Elektroarzt/floragrow/Sense PS/assets/FloraGrow Sense PS PCB bottom.png

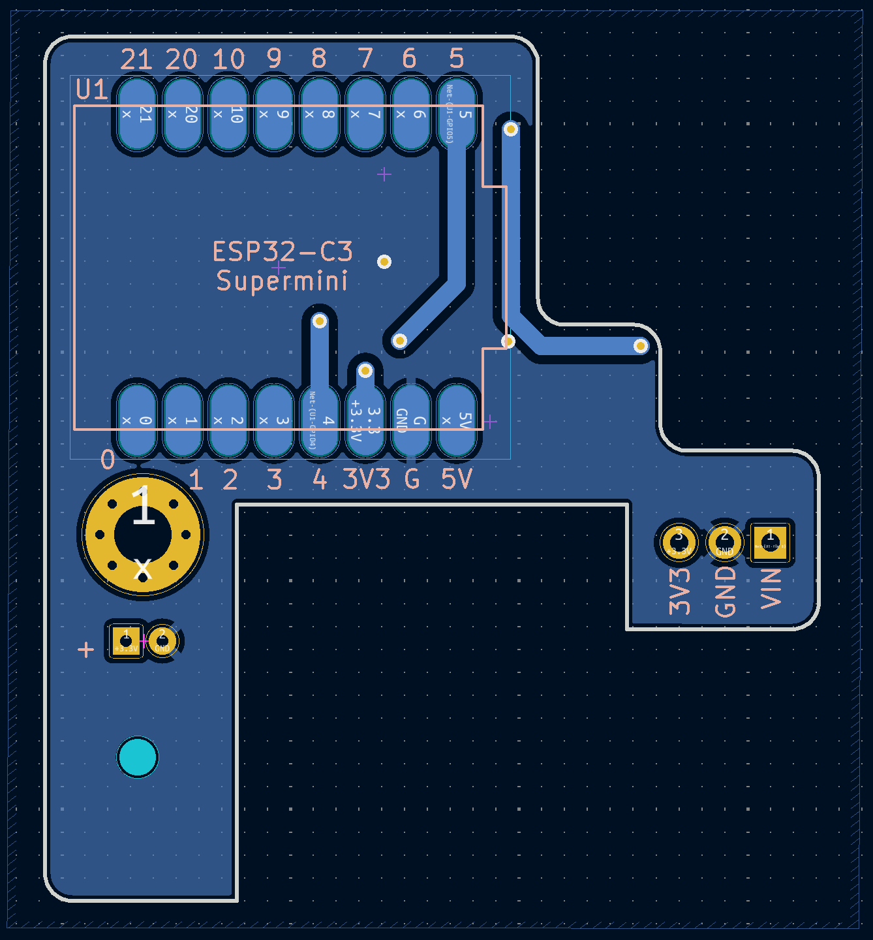
Sense PS/assets/FloraGrow Sense PS PCB bottom.png
