Elektroarzt/floragrow/Sense PS/assets/FloraGrow Sense PS PCB top.png

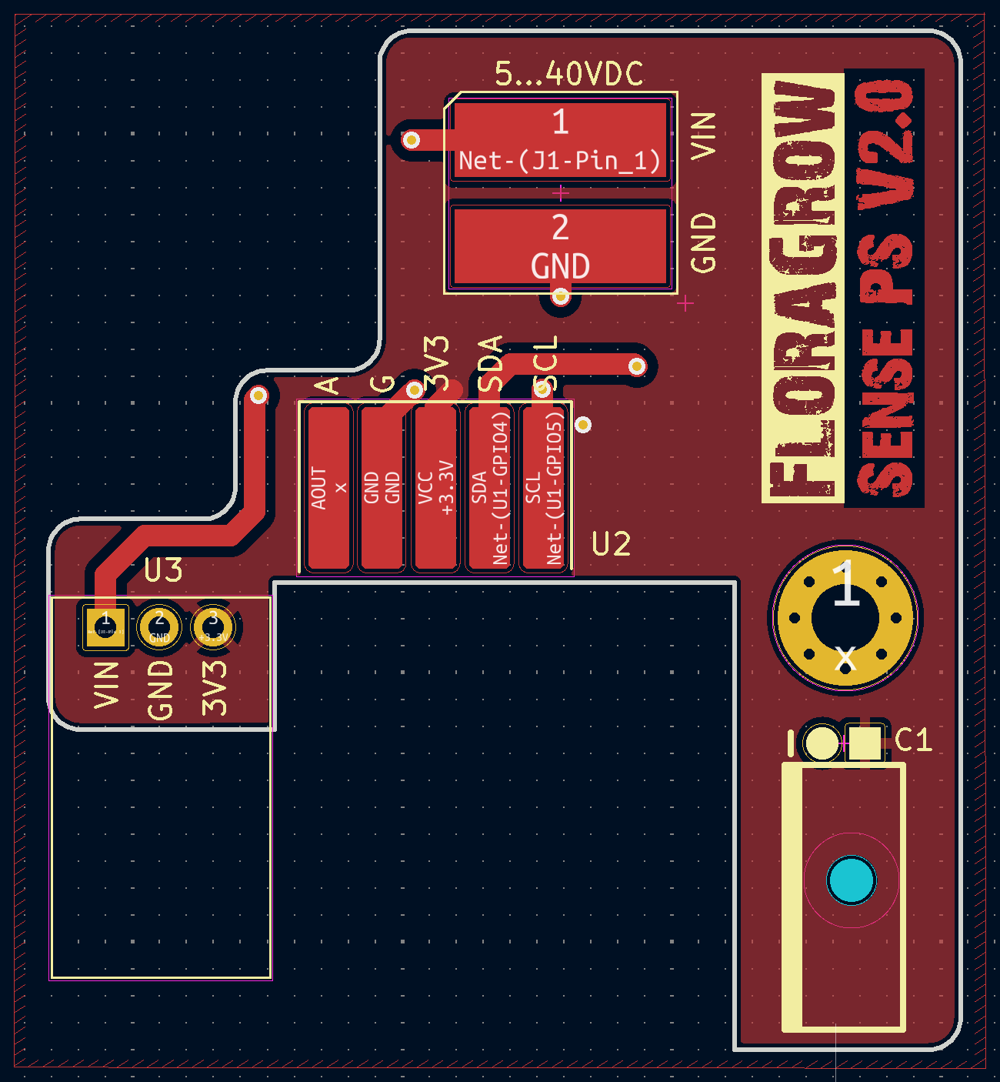
Sense PS/assets/FloraGrow Sense PS PCB top.png
